jurgen178/bitfabrik-trx/hardware/Transceiver.kicad_sch

## KiCad design hardware/Transceiver.kicad_sch (2026-08-04)

Schematic: Transceiver.kicad_sch

Parts:
A1: Arduino_Nano_ESP32; Arduino_Nano
AE1, AE2: Antenna
C1, C7: 39pF
C2, C8: 56pF
C3, C9: 82pF
C4, C10: 150pF
C5, C11, C28: 330pF
C6, C12: 680pF
C13, C14, C16, C22, C39, C43, C61, C69, C70, C77, C80: 10nF
C15, C17, C18, C19, C27, C31, C32, C33, C35, C38, C40, C45, C46, C48, C49, C50, C54, C55, C56, C59, C60, C63, C67, C68, C76, C78, C79, C82, C91, C95, C100: 100nF
C20, C36, C37, C47, C52, C87, C94: 100pF
C21: 22nF
C23, C25: 2200µF/35V
C24, C26, C34, C41, C62, C75: 10uF
C29: 22pF
C30, C51, C53, C81, C85, C86, C92, C96, C97: 1nF
C42: 470uF/50V
C44: 100nF/50V
C57, C58: 130pF
C64, C65: 100µF
C66: 100nF/1000V
C71, C72: 180pF
C73, C74, C88: 10µF
C83, C84: 270pF
C89, C90: 560pF
C93: 470nF
C98, C99: 2,2nF
C101: 1uF
D1, D7, D8, D9, D12: 1N4148; D_DO-35_SOD27_P7.62mm_Horizontal
D2: B40C5000; Diode_Bridge_Round_D9.8mm
D3, D4, D13: BAT85; D_DO-35_SOD27_P7.62mm_Horizontal
D5, D6: BZV55B3V3; D_MiniMELF
D10: 15V; D_MiniMELF
D11: 1N5400; D_DO-201AD_P15.24mm_Horizontal
D14: 1N5819; D_DO-41_SOD81_P10.16mm_Horizontal
D15: D_Schottky
D16: 3,3V; D_MiniMELF
F1: 1A T
F2, F3: 5A F
FL1: 9 MHz SSB Filter; Mini-Circuits_HF1139_LandPatternPL-230
HS1: max 1.4K/W
HS2: max 1K/W
J1: IEC_60320_C14_Receptacle
K1, K4, K11: Relay_SPDT
K2, K12, K13: RX-TX
K3: Relay_DPDT
K5, K14: 10m
K6, K15: 15m
K7, K16: 20m
K8, K17: 40m
K9, K18: 80m
K10, K19: 160m
L1, L13: 0,31µH
L2, L14: 0,41µH
L3, L15: 0,62µH
L4, L16: 1,2µH
L5, L17: 2,5µH
L6, L18: 5µH
L7, L20, L22: 0,22µH
L8, L23, L25: 0,29µH
L9, L28, L30: 0,43µH
L10: 0,82µH
L11: 1,8µH
L12: 3,6µH
L19: 0,88uH
L21: 0,44µH
L24: 0,58µH
L26: 10µH
L27: 100µH
L29: 0,86µH
L31, L33: 1,1µH
L32, L34, L36: 2,2µH
L35, L37, L39: 4,4µH
L38: 8,8µH
LS1, LS2: Speaker
MES1, MES2: Oscilloscope
MK1, MK2: Microphone
Q1, Q3, Q4, Q9: BC547; TO-92_Inline
Q2: 2N2222/Kühlstern
Q5: RD16HHF1
Q6: BD139; TO-126-3_Vertical
Q7: 2N3055; TO-3
Q8: TIC126; TO-220-3_Vertical
Q10: BC557; TO-92_Inline
Q11, Q12, Q14: 2N3904; TO-92_Inline
Q13: 2N2222; TO-92_Inline
R1, R4, R26, R28, R29, R34, R39, R45, R52, R58, R61, R62: 1k
R2, R3: 22k
R5: 560
R6, R36, R40, R53, R59: 220
R7: 240/1W
R8: 22
R9, R10, R12, R21, R22, R23, R24, R37, R48, R49, R50, R51, R56, R57, R64: 10k
R11, R13, R14, R15, R19, R20: 100
R16, R18: 3,3k
R17, R35: 47k
R25: 100k
R27: 3,9k
R30: 2,7k
R31, R44, R46, R65: 4,7k
R32: 5k
R33: 10
R38: 0,1
R41: 12k
R42, R43: 1,5k
R47: 1M
R54: 1,2k
R55: 330
R60: 47
R63: 50
RV1, RV2: 10k
RV3: 100k
SW1: Rotary Encoder KY-040
SW2: Rotary Encoder Bourns EM14R
T1: 120/240V-15V
T2: FT37-43 (20W:1W)
T3: FT37-43 (6W:3W)
T4: FT37-43 (1W:20W bifilar)
T5: FT37-43 (4W:12W)
T6: BN-43-202 (1W:3W)
U1, U6, U11, U12: LM4755TS; TO-263-9_TabPin5
U2: OLED1; ER_OLEDM0.91_1x-I2C
U3, U9, U10: ADE-6; Mini-Circuits_CD542_LandPatternPL-052
U4: AD9850 LO; SSOP-28_5.3x10.2mm_P0.65mm
U5: AD9850 BFO; SSOP-28_5.3x10.2mm_P0.65mm
U7: OLED2; ER_OLEDM0.91_1x-I2C
U8: Touchscreen Display; CR2013-MI2120
U13: MAR-3; SOT-89-3
U14: Produktdetektor SA612
U15: RF Mixer ADE-1; Mini-Circuits_CD542_LandPatternPL-052
U16, U17: TL072
U18: LM723_DIP14; DIP-14_W7.62mm
U19: SA612 (Modulator)
U20: TDA7052A
U21: L7805
U22: MCP23017; SOIC-28W_7.5x17.9mm_P1.27mm
X1, X2, X3: B3715; Filter_SAW_Epcos_DCC6C_3x3mm

Connections:
3,3V: A1.17 (3V3), SW1.2 (VCC), U2.2 (VCC), U7.2 (VCC), U22.9 (V_{DD})
5V: C59.2, C88.1, C91.1, C92.1, C94.1, D14.2 (A), R4.1, R18.2, R26.2, R42.1, R43.1, R48.2, R56.2, U4.6 (DVDD), U4.11 (AVDD), U4.18 (AVDD), U4.23 (DVDD), U5.6 (DVDD), U5.11 (AVDD), U5.18 (AVDD), U5.23 (DVDD), U19.8 (VCC), U21.3 (OUT)
5V / VBUS: SW2.5 (VCC)
9Mhz_SSB_FILTER: FL1.8 (OUT), K13.21
13,8V: C53.2, C54.2, C56.1, C60.2, C73.1, C78.1, C82.2, C85.1, C87.1, D10.1 (K), F2.2, F3.1, L26.2, Q8.1 (K), Q12.3 (C), Q13.3 (C), R9.2, R50.2, R52.2, R58.2, U16.8 (V+)
13.8V: C15.2, C55.1, R7.2, R21.2, U17.8 (V+), U20.1 (VP)
+5V: R5.1
+13.8V: C17.1, C42.1, C44.2, T3.1 (AA), T6.1 (AA)
ADC_FWD: D5.1 (K), R28.2
ADC_REF: D6.1 (K), R29.2, RV3.1
AUDIO_VOLUME_DC: R39.1
Arduino VIN: D14.1 (K)
BNC 50 Ohm: R60.1
D2: A1.5 (D2), R2.1, SW1.5 (CLK), SW2.2 (A)
D3: A1.6 (D3), R3.1, SW1.4 (DT), SW2.6 (B)
DDS_BFO_IN: C20.2, C47.2, U5.21 (IOUT)
DDS_LO_IN: C14.1, C62.2, C63.1, U4.21 (IOUT)
DSB_9MHz_OUT: C80.2, K13.24, U14.1 (IN_A)
ESP32_BAND_SELECT: R1.1, U22.21 (GPA0)
GND: A1.4 (GND), A1.29 (GND), C1.2, C2.2, C3.2, C4.2, C5.2, C6.2, C7.2, C8.2, C9.2, C10.2, C11.2, C12.2, C16.2, C17.2, C19.2, C21.2, C23.2, C24.2, C25.2, C30.1, C31.2, C32.2, C33.1, C34.2, C36.2, C41.2, C42.2, C44.1, C46.2, C49.2, C52.1, C53.1, C54.1, C55.2, C56.2, C57.2, C58.2, C59.1, C60.1, C64.2, C65.2, C66.2, C67.2, C68.2, C70.1, C71.2, C72.2, C73.2, C74.2, C78.2, C79.2, C82.1, C83.2, C84.2, C85.2, C86.2, C87.2, C88.2, C89.2, C90.2, C91.2, C92.2, C93.1, C94.2, C95.1, C96.2, C97.2, C98.2, C99.2, D2.3 (-), D5.2 (A), D6.2 (A), D7.1 (K), D8.2 (A), D11.2 (A), D12.1 (K), FL1.2 (GND), FL1.3 (GND), FL1.4 (GND), FL1.5 (GND), FL1.6 (GND), FL1.7 (GND), MK2.1 (-), Q1.3 (E), Q3.3 (E), Q4.3 (E), Q5.3 (S), Q8.2 (A), Q9.3 (E), R2.2, R3.2, R6.2, R8.2, R10.1, R11.2, R13.2, R14.2, R15.2, R19.1, R20.1, R22.1, R23.2, R24.2, R27.2, R31.2, R32.2, R35.2, R45.2, R47.1, R49.1, R51.1, R53.1, R54.1, R55.1, R57.1, R59.1, R63.1, RV1.3, RV2.1, RV3.3, SW1.1 (GND), SW2.1 (GND), SW2.4 (S2), T2.2 (AB), T2.3 (SA), T3.3 (SA), T5.2 (AB), T5.3 (SA), T6.3 (SA), U2.1 (GND), U4.5 (DGND), U4.10 (AGND), U4.19 (AGND), U4.24 (DGND), U5.5 (DGND), U5.10 (AGND), U5.19 (AGND), U5.24 (DGND), U7.1 (GND), U8.2 (GND), U13.2 (GND), U14.3 (GND), U15.1 (GND), U15.4 (GND), U15.5 (GND), U16.4 (V-), U17.4 (V-), U18.7 (V-), U19.3 (GND), U20.3 (GND), U20.6 (GND), U21.2 (GND), U22.10 (V_{SS})
GNDPWR: C66.1, J1.3 (PE), R47.2
MAIN_MIXER_RF: K12.11, U15.3 (RF)
unnamed: A1.2 (D0/RX), U5.8 (FQ_UD)
unnamed: A1.3 (~RESET), U8.4 (RESET)
unnamed: A1.8 (D5), U4.25 (D7), U5.25 (D7)
unnamed: A1.9 (D6), U4.7 (W_CLK), U5.7 (W_CLK)
unnamed: A1.10 (D7), U4.8 (FQ_UD)
unnamed: A1.11 (D8), U4.22 (RESET), U5.22 (RESET)
unnamed: A1.12 (D9), U8.3 (CS)
unnamed: A1.13 (D10/CS), U8.5 (DC)
unnamed: A1.14 (D11/COPI), U8.6 (MOSI)
unnamed: A1.15 (D12/CIPO), U8.9 (MISO)
unnamed: A1.16 (D13/SCK), U8.7 (SCK)
unnamed: A1.23 (SDA/A4), U2.4 (SDA), U7.4 (SDA), U8.10 (SDA), U22.13 (SDA)
unnamed: A1.24 (SCL/A5), U2.3 (SCL), U7.3 (SCL), U8.11 (SCL), U22.12 (SCK)
unnamed: AE2.1, K2.11
unnamed: C1.1, L1.2, L7.1
unnamed: C2.1, L2.2, L8.1
unnamed: C3.1, L3.2, L9.1
unnamed: C4.1, L4.2, L10.1
unnamed: C5.1, L5.2, L11.1
unnamed: C6.1, L6.2, L12.1
unnamed: C7.1, L7.2, L13.1
unnamed: C8.1, L8.2, L14.1
unnamed: C9.1, L9.2, L15.1
unnamed: C10.1, L10.2, L16.1
unnamed: C11.1, L11.2, L17.1
unnamed: C12.1, L12.2, L18.1
unnamed: C13.2, Q2.B, R5.2, R6.1
unnamed: C14.2, U13.1
unnamed: C15.1, C22.1, R7.1, U13.3
unnamed: C16.1, C18.1, MK2.2 (+), R4.2
unnamed: C18.2, RV1.1
unnamed: C19.1, U14.2 (IN_B)
unnamed: C20.1, U14.6 (B)
unnamed: C21.1, Q2.E, R8.1
unnamed: C22.2, U15.6 (LO)
unnamed: C23.1, C25.1, C30.2, C33.2, D2.1 (+), R38.1, U18.2 (ILIM), U18.11 (VC), U18.12 (V+)
unnamed: C24.1, R9.1, R10.2, U16.3 (+), U16.5 (+)
unnamed: C26.1, R25.2, U16.2 (-)
unnamed: C26.2, R12.1
unnamed: C27.1, U14.4 (OUT_A)
unnamed: C27.2, R17.2, U17.3 (+)
unnamed: C28.1, C29.1, U15.2 (IF)
unnamed: C28.2, C29.2, C35.1, L19.1
unnamed: C31.1, D3.1 (K), R23.1, R28.1
unnamed: C32.1, D4.1 (K), R24.1, R29.1
unnamed: C34.1, R17.1, R21.1, R22.2, U17.5 (+)
unnamed: C35.2, T5.1 (AA)
unnamed: C37.1, R27.1, R41.2, U18.4 (-)
unnamed: C37.2, U18.13 (FC)
unnamed: C38.1, R25.1, U16.1
unnamed: C39.1, C40.1, T3.4 (SB)
unnamed: C41.1, R34.2
unnamed: C43.1, R36.1
unnamed: C43.2, Q5.1 (G), R33.2, R35.1
unnamed: C45.2, U19.1 (IN_A)
unnamed: C46.1, U19.2 (IN_B)
unnamed: C47.1, U19.6 (B)
unnamed: C48.1, R37.2, U17.1
unnamed: C48.2, U20.2 (+)
unnamed: C49.1, R39.2, U20.4 (V)
unnamed: C50.1, T6.4 (SB)
unnamed: C51.1, R42.2, U19.4 (OUT_A)
unnamed: C52.2, D10.2 (A), Q8.3 (G), R45.1
unnamed: C57.1, L20.1, L21.2
unnamed: C58.1, L21.1, L22.2
unnamed: C61.2, Q11.2 (B), R48.1, R49.2
unnamed: C62.1, C63.2, Q12.2 (B), R50.1, R51.2
unnamed: C64.1, C65.1, C67.1, C68.1, D11.1 (K), F3.2, L26.1, L27.1
unnamed: C69.1, Q11.3 (C), R52.1
unnamed: C69.2, Q14.2 (B), R56.1, R57.2
unnamed: C70.2, Q11.1 (E), R53.2
unnamed: C71.1, L23.1, L24.2
unnamed: C72.1, L24.1, L25.2
unnamed: C74.1, C79.1, C86.1, L27.2, U21.1 (IN)
unnamed: C75.1, C76.1, Q13.1 (E), R55.2
unnamed: C75.2, C76.2, R60.2
unnamed: C77.1, D12.2 (A), R61.2
unnamed: C77.2, Q14.1 (E), R59.2
unnamed: C80.1, C81.1, Q14.3 (C), R58.1
unnamed: C83.1, L28.1, L29.2
unnamed: C84.1, L29.1, L30.2
unnamed: C89.1, L31.1, L32.2
unnamed: C90.1, L32.1, L33.2
unnamed: C96.1, L34.1, L35.2
unnamed: C97.1, L35.1, L36.2
unnamed: C98.1, L37.1, L38.2
unnamed: C99.1, L38.1, L39.2
unnamed: C100.1, D15.2 (A), R64.2
unnamed: C36.1, C38.2, C45.1, C100.2, D7.2 (A), D8.1 (K)
unnamed: C101.1, D15.1 (K), R65.1
unnamed: D1.2 (A), K3.A2, Q1.1 (C)
unnamed: D2.2, T1.1 (AA)
unnamed: D2.4, T1.2 (AB)
unnamed: D3.2 (A), R14.1, R15.1, T4.5 (SB)
unnamed: D4.2 (A), R11.1, R13.1, T4.3 (SA)
unnamed: D9.1 (K), Q9.1 (C), Q10.2 (B), R46.2
unnamed: F1.1, J1.1 (L)
unnamed: F1.2, T1.4 (SB), T1.6 (SD)
unnamed: F2.1, Q7.2 (E), R40.1, R41.1
unnamed: FL1.1 (IN), T5.4 (SB)
unnamed: J1.2 (N), T1.3 (SA), T1.5 (SC)
unnamed: K5.14, L1.1
unnamed: K5.24, L13.2
unnamed: K6.14, L2.1
unnamed: K6.24, L14.2
unnamed: K7.14, L3.1
unnamed: K7.24, L15.2
unnamed: K8.14, L4.1
unnamed: K8.24, L16.2
unnamed: K9.14, L5.1
unnamed: K9.24, L17.2
unnamed: K10.14, L6.1
unnamed: K10.24, L18.2
unnamed: K14.12, K15.11
unnamed: K14.14, L22.1
unnamed: K14.22, K15.21
unnamed: K14.24, L20.2
unnamed: K15.12, K16.11
unnamed: K15.14, L25.1
unnamed: K15.22, K16.21
unnamed: K15.24, L23.2
unnamed: K16.12, K17.11
unnamed: K16.14, L30.1
unnamed: K16.22, K17.21
unnamed: K16.24, L28.2
unnamed: K17.12, K18.11
unnamed: K17.14, L33.1
unnamed: K17.22, K18.21
unnamed: K17.24, L31.2
unnamed: K18.12, K19.11
unnamed: K18.14, L36.1
unnamed: K18.22, K19.21
unnamed: K18.24, L34.2
unnamed: K19.12, R63.2
unnamed: K19.14, L39.1
unnamed: K19.24, L37.2
unnamed: L19.2, R19.2, R20.2
unnamed: LS2.1, U20.5
unnamed: LS2.2, U20.8
unnamed: Q1.2 (B), R1.2
unnamed: Q2.C, T3.2 (AB)
unnamed: Q3.1 (C), Q4.2 (B), R18.1
unnamed: Q3.2 (B), R16.1
unnamed: Q4.1 (C), R26.1, RV2.3
unnamed: Q5.2 (D), R36.2, T6.2 (AB)
unnamed: Q6.1 (E), Q7.1 (B), R40.2
unnamed: Q6.2 (C), Q7.3 (C), R38.2, U18.3 (CSEN)
unnamed: Q6.3 (B), U18.10 (Vout)
unnamed: Q9.2 (B), Q10.1 (C), RV3.2
unnamed: Q10.3 (E), R44.1, R46.1
unnamed: Q12.1 (E), Q13.2 (B), R54.2
unnamed: R12.2, RV1.2
unnamed: R30.1, U18.6 (VREF)
unnamed: R30.2, R31.1, R32.1, U18.5 (+)
unnamed: R34.1, R37.1, U17.2 (-)
unnamed: R43.2, U19.5 (OUT_B)
unnamed: T2.1 (AA), T4.4 (SC)
unnamed: U3.4, U3.5
unnamed: U9.4, U9.5
unnamed: U10.4, U10.5
unnamed: U16.6 (-), U16.7
unnamed: U17.6 (-), U17.7
unnamed: X1.3, X1.4, X1.6
unnamed: X2.3, X2.4, X2.6
unnamed: X3.3, X3.4, X3.6
PA_GATE: C39.2, C40.2, D9.2 (A), R33.1, RV2.2
PTT: D16.1 (K), R65.2
RX_FILTER_IN: K2.12, K5.11, K6.11, K7.11, K8.11, K9.11, K10.11
RX_FILTER_OUT: K5.21, K6.21, K7.21, K8.21, K9.21, K10.21, K12.12
RX_MIXER_IN: C51.2, C61.1, K13.22
SW: A1.7 (D4), SW1.3 (SW), SW2.3 (S1)
SWR_TX_OUT: K2.14, T2.4 (SB), T4.2 (AB)
S_METER_IN: C95.2, D13.1 (K)
S_METER_OUT: C81.2, D13.2 (A)
TX_FILTER_IN: C50.2, K14.11
TX_FILTER_OUT: K14.21, T4.1 (AA)
TX_MIXER_OUT: C13.1, K12.14
TX_PA_ACTIVE: R16.2, R44.2
VBUS: A1.27 (VUSB/5V), U8.1 (VCC), U8.8 (LED)
VCC: D1.1 (K), K3.A1
ZF_AGC: C93.2, R61.1, R62.2
ZF_PWR_CTRL: R62.1

Notes on the sheet:
TX Tiefpassfilter
Modularer Kurzwellen‑SSB‑Transceiver
Netzteil, Extern
Stockton Richtkoppler
Mischer- und ZF-Stufe
Power In
TX Modulator
Produktdetektor / NF
PA SWR overload protection
für Signalgenerator BNC 50 Ohm
ZF Verstärker
RX Bandfilter
