jurgen178/bitfabrik-trx/src/Globals.h

#ifndef GLOBALS_H
#define GLOBALS_H

/**
 * ── BITFABRIK Transceiver v3.0 ──────────────────────────────────────────
 * Global State, Object Instances, and Shared Structures.
 * ──────────────────────────────────────────────────────────────────────────
 */

#include <Arduino.h>
#include <Adafruit_SSD1306.h>
#include <ArduinoJson.h>
#define LGFX_USE_V1
#include <LovyanGFX.hpp>
#include <Adafruit_MCP23X17.h>
#include <Preferences.h>
#include <ESPAsyncWebServer.h>
#include <atomic>
#include "Constants.h"

// ── LovyanGFX Driver Configuration (Hosyond 4.0" TN) ────────────────────────
class LGFX_TRX : public lgfx::LGFX_Device
{
  lgfx::Panel_ST7796  panelInstance;
  lgfx::Bus_SPI       busInstance;
  lgfx::Touch_FT5x06  touchInstance; // Compatible with FT6336U

public:
  LGFX_TRX()
  {
    {
      auto cfg = busInstance.config();
      cfg.spi_host = SPI3_HOST;
      cfg.spi_mode = 0;
      cfg.freq_write = 20000000;
      cfg.freq_read  = 8000000;
      cfg.pin_sclk = TFT_SCK;
      cfg.pin_mosi = TFT_MOSI;
      cfg.pin_miso = TFT_MISO;
      cfg.pin_dc   = TFT_DC;
      busInstance.config(cfg);
      panelInstance.setBus(&busInstance);
    }
    {
      auto cfg = panelInstance.config();
      cfg.pin_cs           = TFT_CS;
      cfg.pin_rst          = TFT_RST; // Pin A0
      cfg.panel_width      = 320;
      cfg.panel_height     = 480;
      cfg.bus_shared       = true;
      panelInstance.config(cfg);
    }
    {
      auto cfg = touchInstance.config();
      cfg.x_min      = 0;
      cfg.x_max      = 319;
      cfg.y_min      = 0;
      cfg.y_max      = 479;
      cfg.pin_sda    = 11; // A4
      cfg.pin_scl    = 12; // A5
      cfg.i2c_port   = 0;  // Shared I2C port
      cfg.i2c_addr   = 0x38;
      cfg.freq       = 400000;
      touchInstance.config(cfg);
      panelInstance.setTouch(&touchInstance);
    }
    setPanel(&panelInstance);
  }
};

// ── Data Structures ────────────────────────────────────────────────────────

struct Band
{
  char        name[16];   // Anzeige-Name (z.B. "40m")
  long        freqMin;    // Untere Grenze für diesen Filter
  long        freqMax;    // Obere Grenze für diesen Filter
  long        freqDefault;// Startfrequenz
  int         rxRelay;    // Physischer Slot (0-5) für Empfang
  int         txRelay;    // Physischer Slot (0-5) für Senden
  bool        sideBand;   // true = USB, false = LSB (Dynamic)
  bool        enabled;    // Ob dieser Slot bestückt/aktiv ist
};

struct VfoState
{
  long freq;
  int  band;
  bool usb;
  volatile bool occupied; // volatile: written by Core 0 (web), read by Core 1 (radio)
};

struct SWRResult
{
  float swr;
  float powerW;
  float vFwd;
  float vRef;
  float rssi;   // Voltage from receiver (0-3.3V)
  int   sLevel; // S-Unit (1-9)
};

/**
 * ── DECOUPLED SYNC STATE ──────────────────────────────────────────────────
 * Shared memory bridge between Network (Core 0) and Radio (Core 1).
 * Prevents Bus conflicts by ensuring only Core 1 touches hardware.
 * ──────────────────────────────────────────────────────────────────────────
 */
struct SyncState
{
    // ── Commands (Written by Web, Read by Radio) ──
    std::atomic<long> targetFreq;
    std::atomic<int>  targetBand;
    std::atomic<int>  targetVfo;
    std::atomic<long> targetRitOffset;
    std::atomic<int>  targetStepIdx;
    std::atomic<int>  targetDigiMode;
    std::atomic<int>  targetVol;
    std::atomic<int>  targetPwr;
    std::atomic<int>  targetMic;
    std::atomic<int>  targetVoxThresh;
    std::atomic<int>  targetVoxDelay;

    // Command Flags (which parameter to update)
    std::atomic<uint32_t> updateMask;
    std::atomic<bool>     updatePending;

    // ── Metrics (Written by Radio, Read by Web) ──
    std::atomic<float> swr;
    std::atomic<float> pwrW;
    std::atomic<float> rssi;
    std::atomic<int>   sLevel;

    // ── Status Mirror (Written by Radio, Read by Web) ──
    // This allows the Web to build JSON without touching Engine objects
    std::atomic<long> currFreq;
    std::atomic<int>  currBand;
    std::atomic<bool> currUsb;
    std::atomic<int>  currVfo;
    std::atomic<bool> currRitEn;
    std::atomic<long> currRitOff;
    std::atomic<bool> currVoxEn;
    std::atomic<int>  currVoxThresh;
    std::atomic<int>  currVoxDelay;
    std::atomic<int>  currVol;
    std::atomic<int>  currPwr;
    std::atomic<int>  currMic;
    std::atomic<long> currMinFreq;
    std::atomic<long> currMaxFreq;
    std::atomic<long> currStepVal;
    std::atomic<int>  currDigiMode;
    std::atomic<int>  currModeIdx; // 0=RADIO, 1=GEN, 2=SETTINGS, 3=RIT
    std::atomic<bool> currBusy;
    std::atomic<bool> currTx;
    std::atomic<bool> vfoCopyFlash; // Set true briefly when A=B happens

    // Memory mirror for tooltips
    struct MemEntry {
        std::atomic<long> freq;
        std::atomic<int>  band;
        std::atomic<bool> occ;
    } memMirror[NUM_MEM_CHANNELS];
    std::atomic<uint32_t> memRevision; // Mirror of radio.getMemRevision()
};

// Masks for updateMask
#define SYNC_FREQ       (1 << 0)
#define SYNC_BAND       (1 << 1)
#define SYNC_VFO        (1 << 2)
#define SYNC_RIT        (1 << 3)
#define SYNC_STEP       (1 << 4)
#define SYNC_DIGI       (1 << 5)
#define SYNC_VOL        (1 << 6)
#define SYNC_PWR        (1 << 7)
#define SYNC_MIC        (1 << 8)
#define SYNC_VOX        (1 << 9)
#define SYNC_MODE       (1 << 10) // DisplayMode switch
#define SYNC_VFO_COPY   (1 << 11)
#define SYNC_MEM_STORE  (1 << 12)
#define SYNC_MEM_RECALL (1 << 13)
#define SYNC_NO_UI      (1 << 14) // Do not trigger UI mode switches (for Automation/REST)

extern SyncState g_sync;

// ── Shared Enumerations ──────────────────────────────────────────────────

enum class EncoderMode
{
    Tune,
    Volume,
    Power,
    Mic,
    Calibrate,
    Rit
};

// ── Global State Variables (Shared between Cores) ──────────────────────────

extern std::atomic<bool> g_tx;
extern std::atomic<bool> g_mcpOk;
extern std::atomic<unsigned long> g_lastActivityTime;

// UI Synchronization Flags
extern std::atomic<bool> g_guiNeedsUpdate;   // VFO/Status changed → triggers TFT refresh
extern TaskHandle_t  g_networkTaskHandle;    // Set by TaskNetwork — used for event wakeup

// System Performance Metrics
extern volatile int g_cpuLoad0; // Core 0 utilization (%)
extern volatile int g_cpuLoad1; // Core 1 utilization (%)
extern volatile int g_wifiRssi;  // Signal strength in dBm
extern volatile int g_webClients; // Number of connected WS clients
extern volatile int g_netActivity; // Packets per second (TX+RX)

// Encoder Accumulators
extern volatile int  g_encPos;
extern volatile unsigned long g_lastEncMove;
extern volatile unsigned long g_encInterval; // Time between last two pulses
extern volatile uint8_t g_oldEncState;
extern volatile int8_t  s_encAccum;
extern const int8_t ENC_STATES[];

// ── Hardware Object Singletons ──────────────────────────────────────────────

extern LGFX_TRX tft;
extern Adafruit_SSD1306 display1;
extern Adafruit_SSD1306 display2;
extern Adafruit_MCP23X17 mcp;
extern Preferences preferences;

// Forward declaration of the Manager
class EncoderManager;
extern EncoderManager encManager;

class RadioEngine;
extern RadioEngine radio;

class AudioManager;
extern AudioManager audio;

class SettingsManager;
extern SettingsManager settings;

// Concurrency
extern SemaphoreHandle_t g_mutex;
extern SemaphoreHandle_t g_hwMutex;

// ── Shared Function Prototypes ─────────────────────────────────────────────

SWRResult readSWR();

// ── Constant Arrays ────────────────────────────────────────────────────────

extern Band BANDS[]; // Now dynamic (loaded from JSON)
extern const long STEPS[];

#endif
